elmo2k3/dabpi_ctl/doc/pics/IMG_0292.JPG

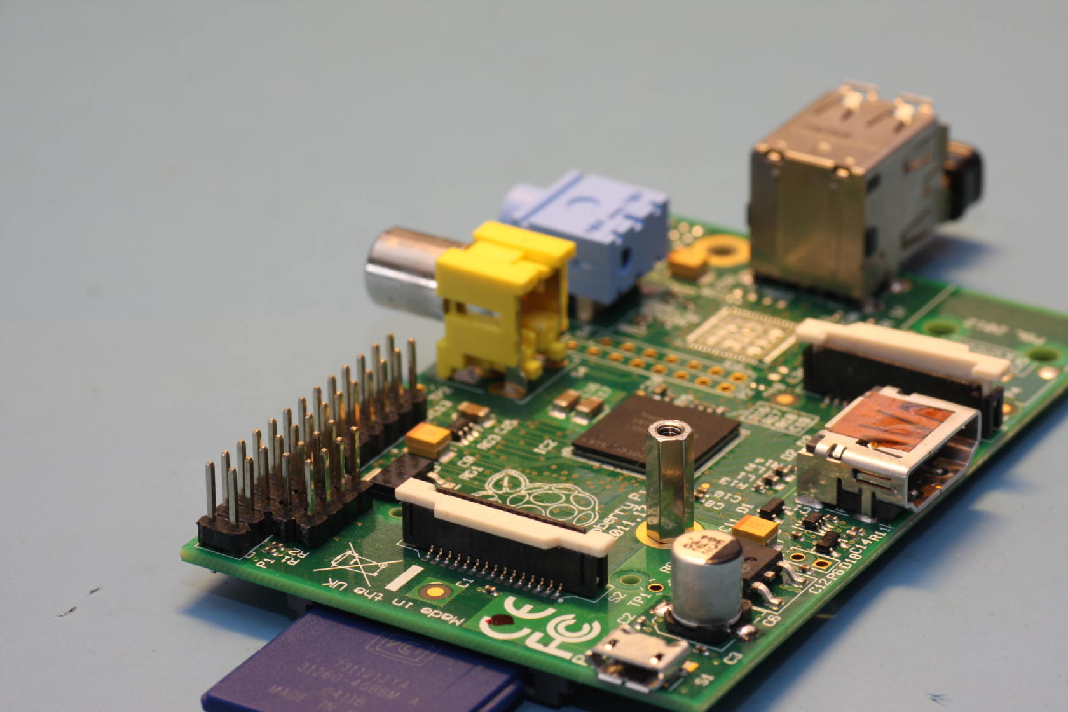
doc/pics/IMG_0292.JPG
